mrbichel/TheTree/electronics/3leds/inseries_etch_silk_bottom.pdf

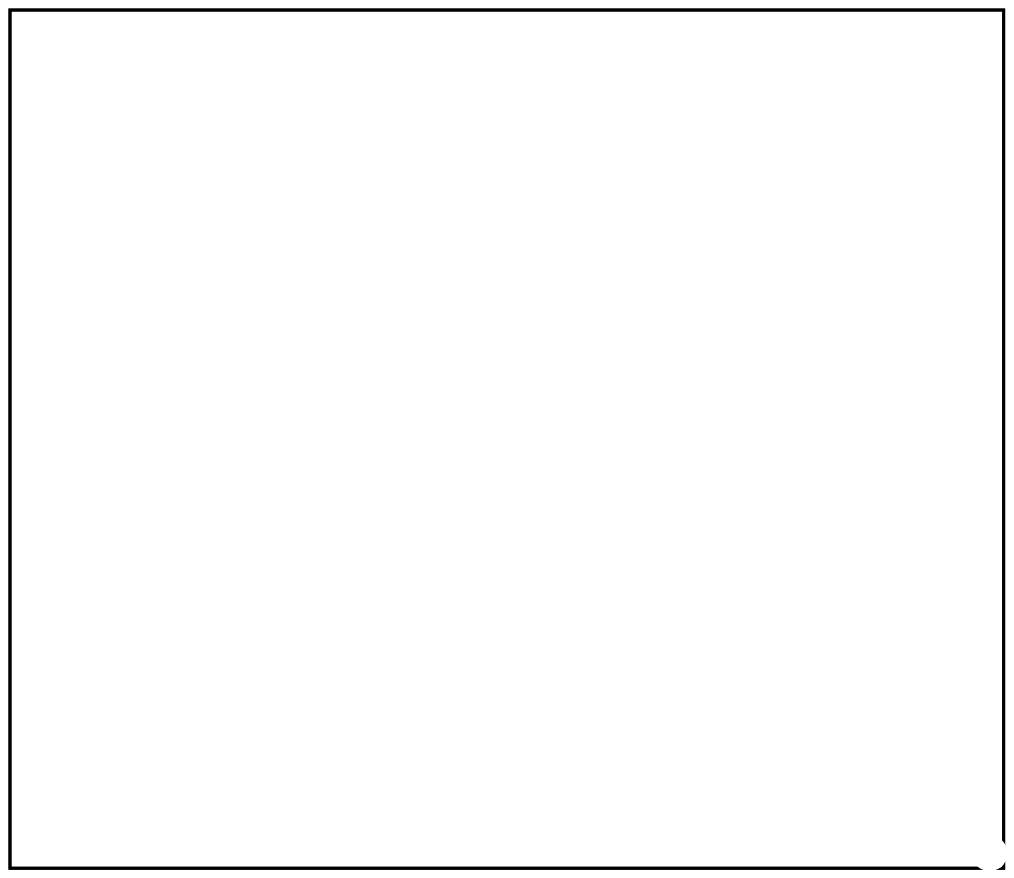
[picture p5: page 1]
