mrbichel/TheTree/electronics/3leds/inseries_etch_silk_bottom_mirror.pdf

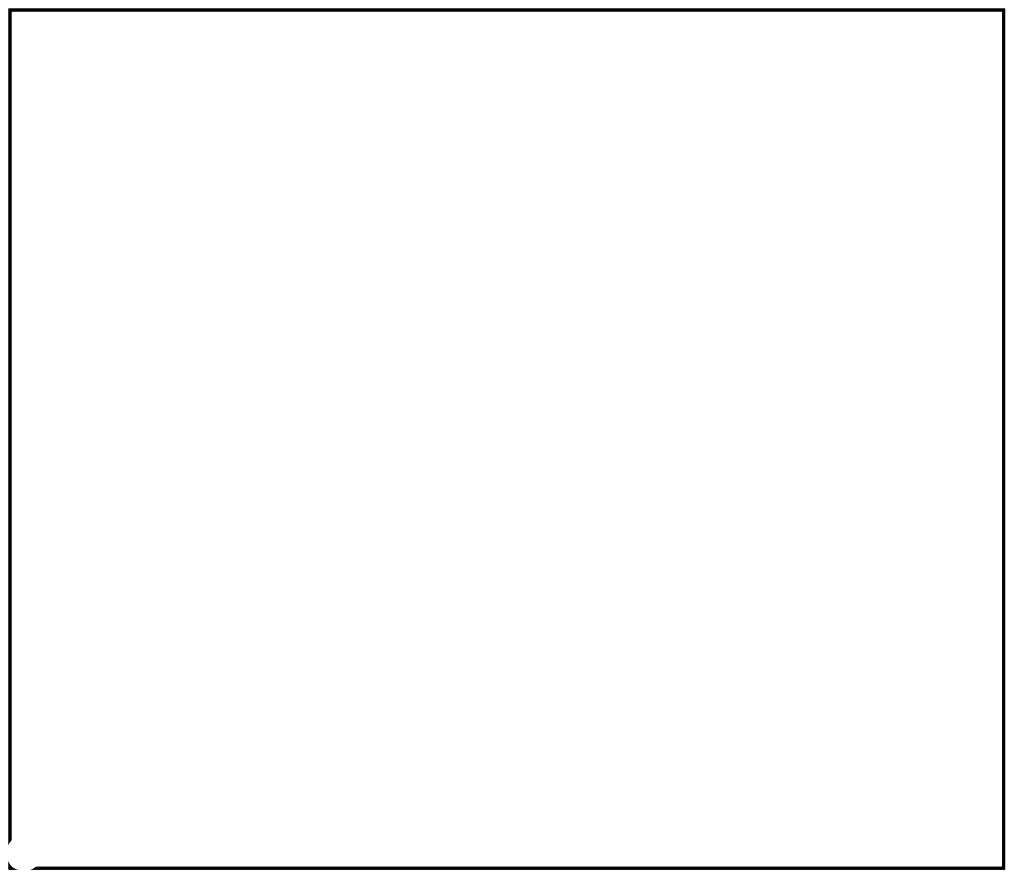
[picture p6: page 1]
