mrbichel/TheTree/electronics/3leds/inseries_etch_silk_top.pdf

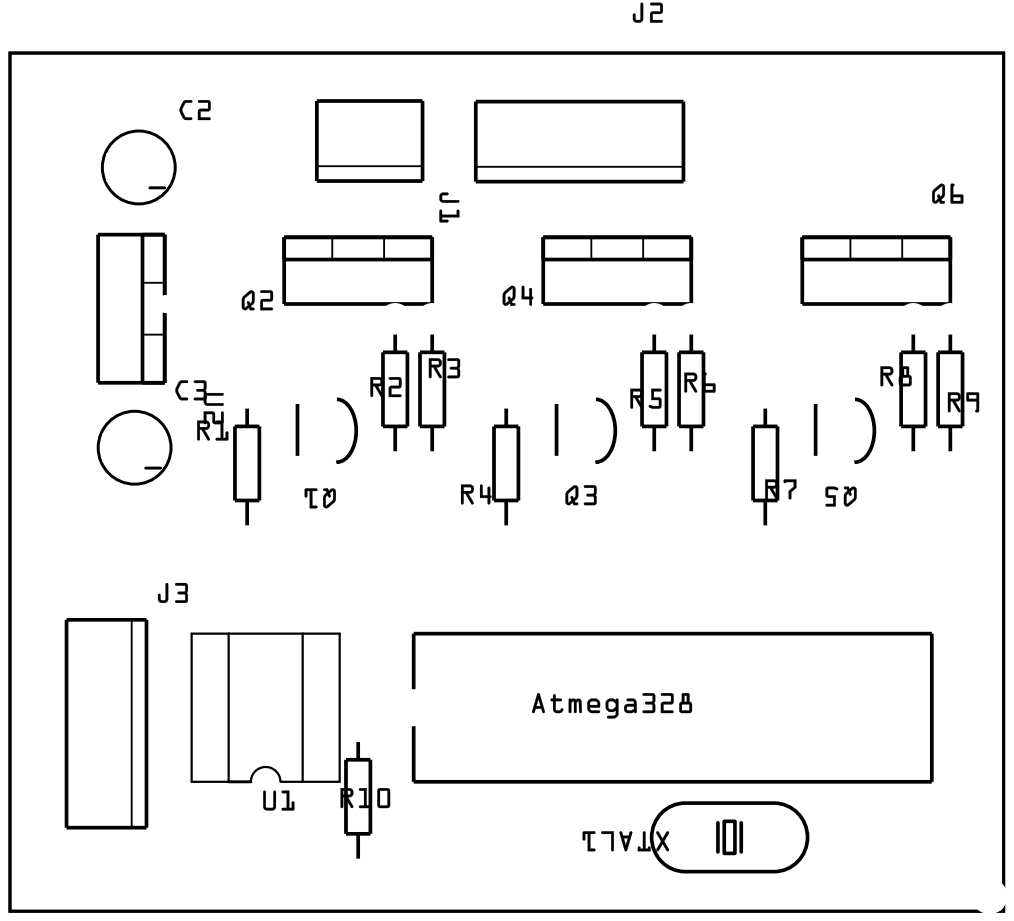
[picture p13: page 1]
