mrbichel/TheTree/electronics/3leds/inseries_etch_silk_top_mirror.pdf

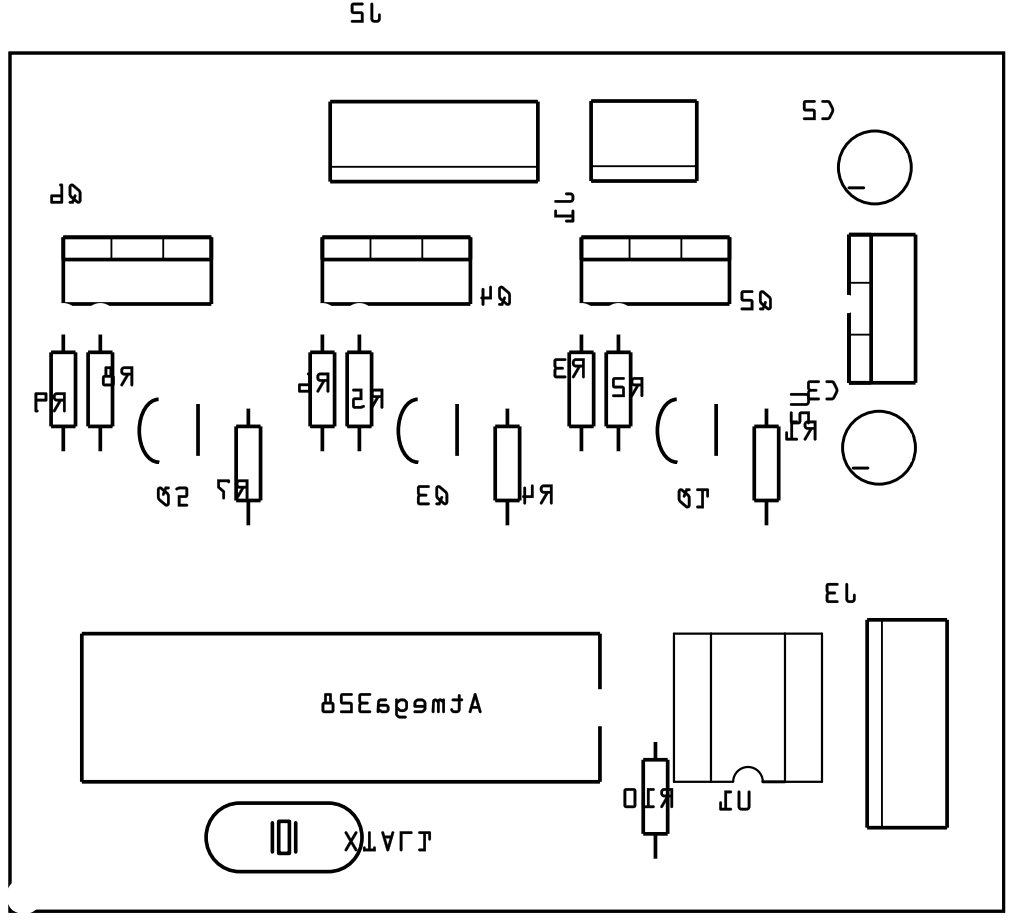
[picture p14: page 1]
